MarkAhlbrecht/DasBoot/code/python/resources/HeadingIndicator_Needle.png

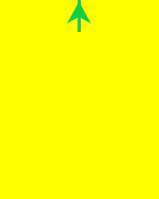
code/python/resources/HeadingIndicator_Needle.png
