MarkAhlbrecht/DasBoot/data/MagData_long_static.PNG

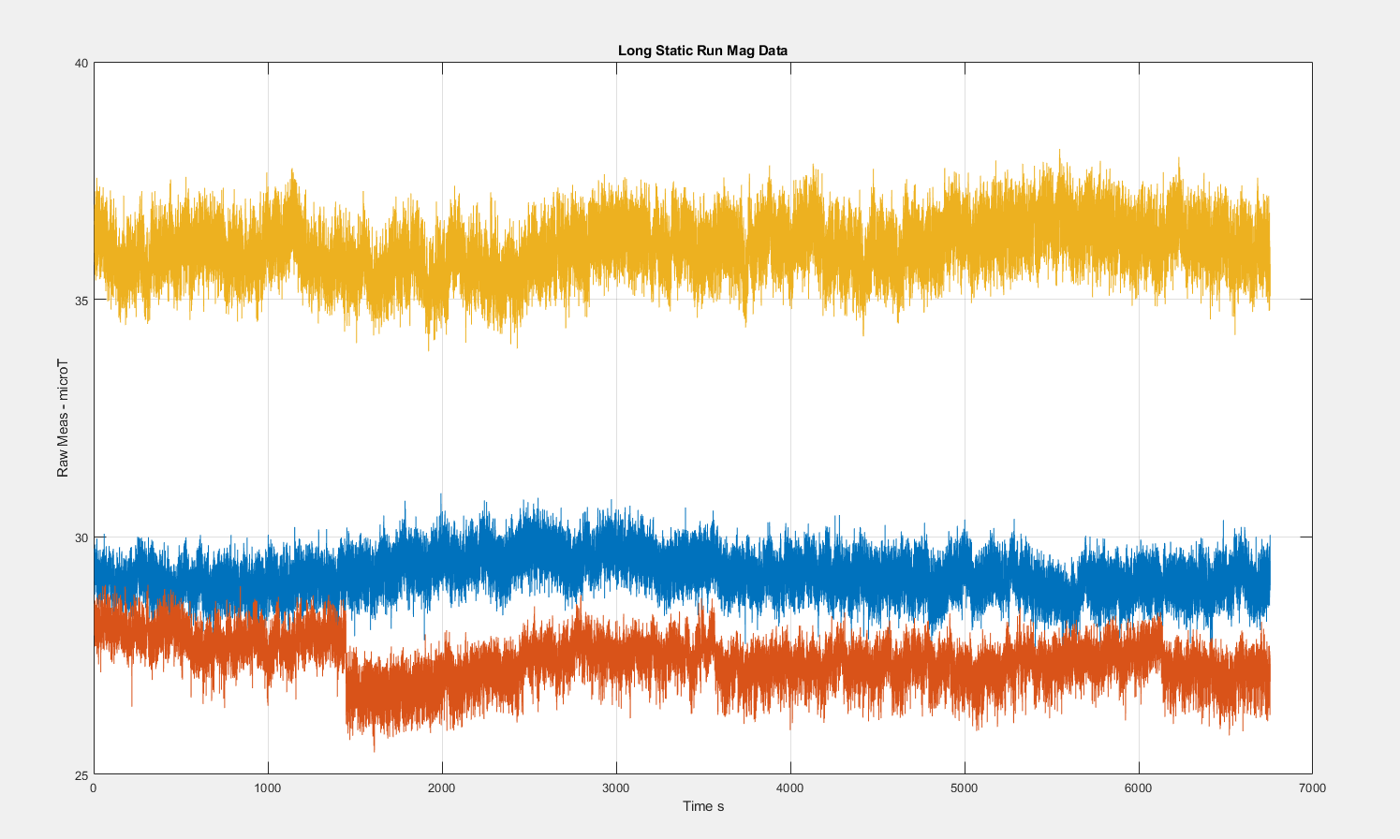
data/MagData_long_static.PNG
