MarkAhlbrecht/DasBoot/code/python/SharpMemory/lcd_ip_addr.py

"""
This demo will fill the screen with white, draw a black box on top
and then print Hello World! in the center of the display

This example is for use on (Linux) computers that are using CPython with
Adafruit Blinka to support CircuitPython libraries. CircuitPython does
not support PIL/pillow (python imaging library)!
"""

import board
import busio
import digitalio
from PIL import Image, ImageDraw, ImageFont
import adafruit_sharpmemorydisplay
import time
import socket

# Colors
BLACK = 0
WHITE = 255

# Parameters to Change
BORDER = 3
FONTSIZE = 50

try:
    testIP = "8.8.8.8"
    s = socket.socket(socket.AF_INET, socket.SOCK_DGRAM)
    s.connect((testIP, 0))
    ipaddr = s.getsockname()[0]
    host = socket.gethostname()
    print ("IP:", ipaddr, " Host:", host)
except:
    ipaddr = "0.0.0.0"
    host = "Fail"

spi = busio.SPI(board.SCK, MOSI=board.MOSI)
scs = digitalio.DigitalInOut(board.D22)  # inverted chip select

# display = adafruit_sharpmemorydisplay.SharpMemoryDisplay(spi, scs, 96, 96)
display = adafruit_sharpmemorydisplay.SharpMemoryDisplay(spi, scs, 400, 240)

# Clear display.
display.fill(1)
display.show()



# Create blank image for drawing.
# Make sure to create image with mode '1' for 1-bit color.
image = Image.new("1", (display.width, display.height))

# Get drawing object to draw on image.
draw = ImageDraw.Draw(image)

# Draw a black background
draw.rectangle((0, 0, display.width, display.height), outline=BLACK, fill=BLACK)

# Draw a smaller inner rectangle
draw.rectangle(
    (BORDER, BORDER, display.width - BORDER - 1, display.height - BORDER - 1),
    outline=WHITE,
    fill=WHITE,
)

# Load a TTF font.
font = ImageFont.truetype("/usr/share/fonts/truetype/dejavu/DejaVuSans.ttf", 15)
counterFont = ImageFont.truetype("/usr/share/fonts/truetype/dejavu/DejaVuSans.ttf", FONTSIZE)

display.fill(1)
display.text(host +": ", 40, 75, 0,  size=4)
display.text(ipaddr, 40, 125, 0,  size=4)
display.show()
